RubenTrov/Microll/Simulations/RGB_LED.asc

Blue: res; 330
Green: res; 330
Red: res; 330
Vf_blue: voltage; 2.65
Vf_green: voltage; 2.65
Vf_red: voltage; 1.8
Named nets: 0
.tran 1
LED: APTF1616LSEEZGKQBKC
RGB Led
Simulating current using resistors and Vf from datasheet
